Breadstick-Innovations/M4-Breadstick/Examples/4. Button/IMG_8299.JPG

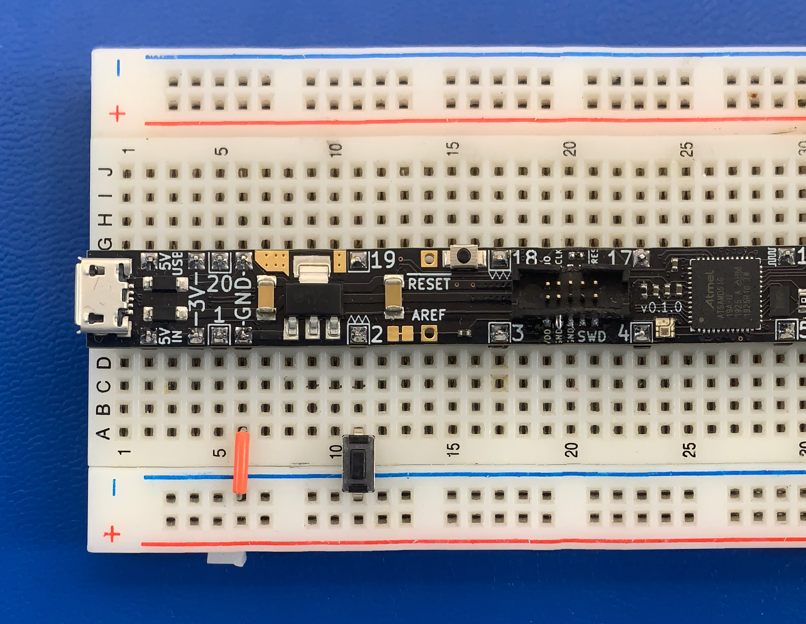
Examples/4. Button/IMG_8299.JPG
