Breadstick-Innovations/M4-Breadstick/Examples/5. Dual I2C Display/IMG_3248.jpg

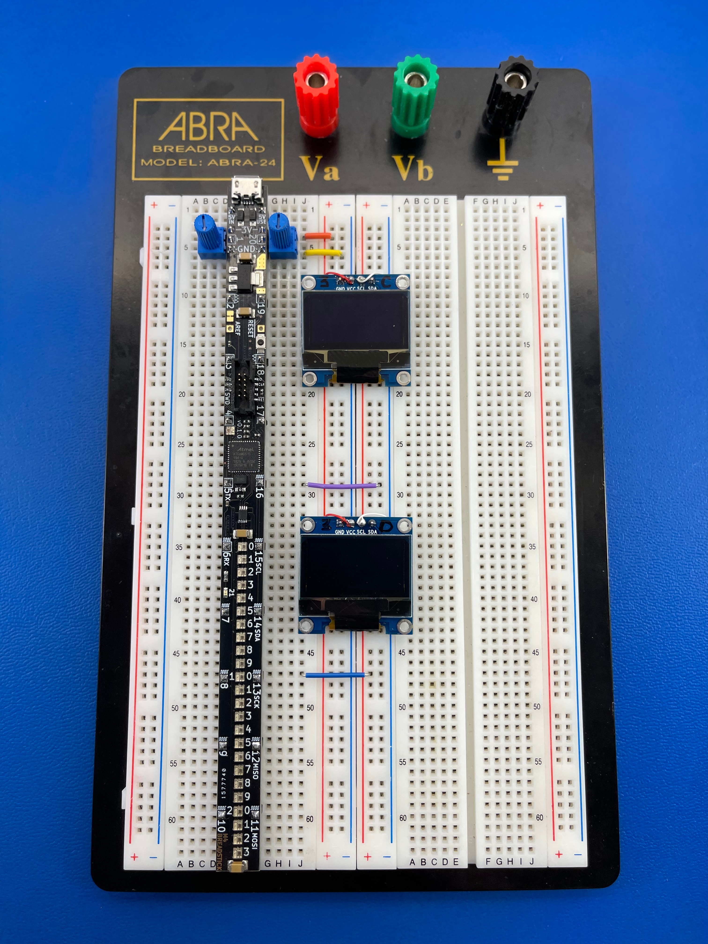
Examples/5. Dual I2C Display/IMG_3248.jpg
