Breadstick-Innovations/M4-Breadstick/Examples/6. Many Pots/IMG_8300.JPG

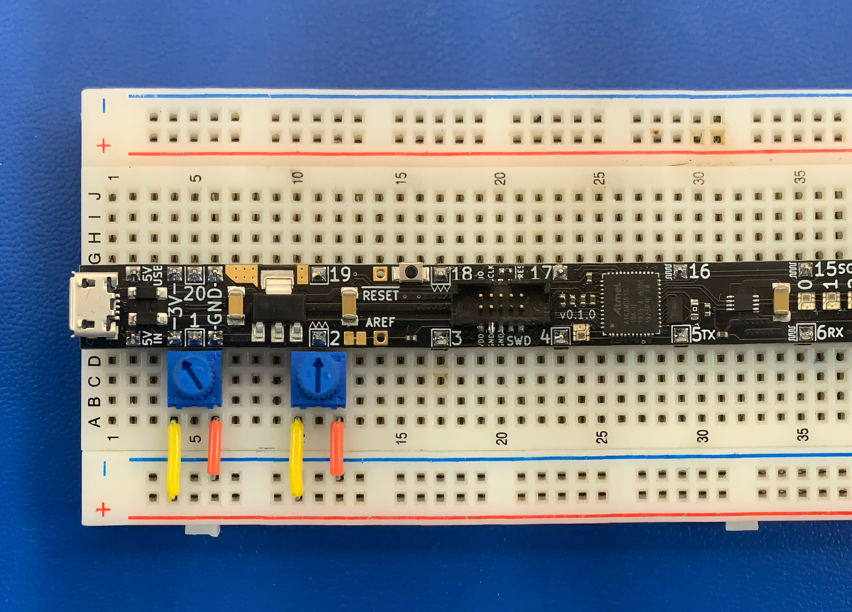
Examples/6. Many Pots/IMG_8300.JPG
