Breadstick-Innovations/M4-Breadstick/Examples/7. Many Buttons/IMG_8317.JPG

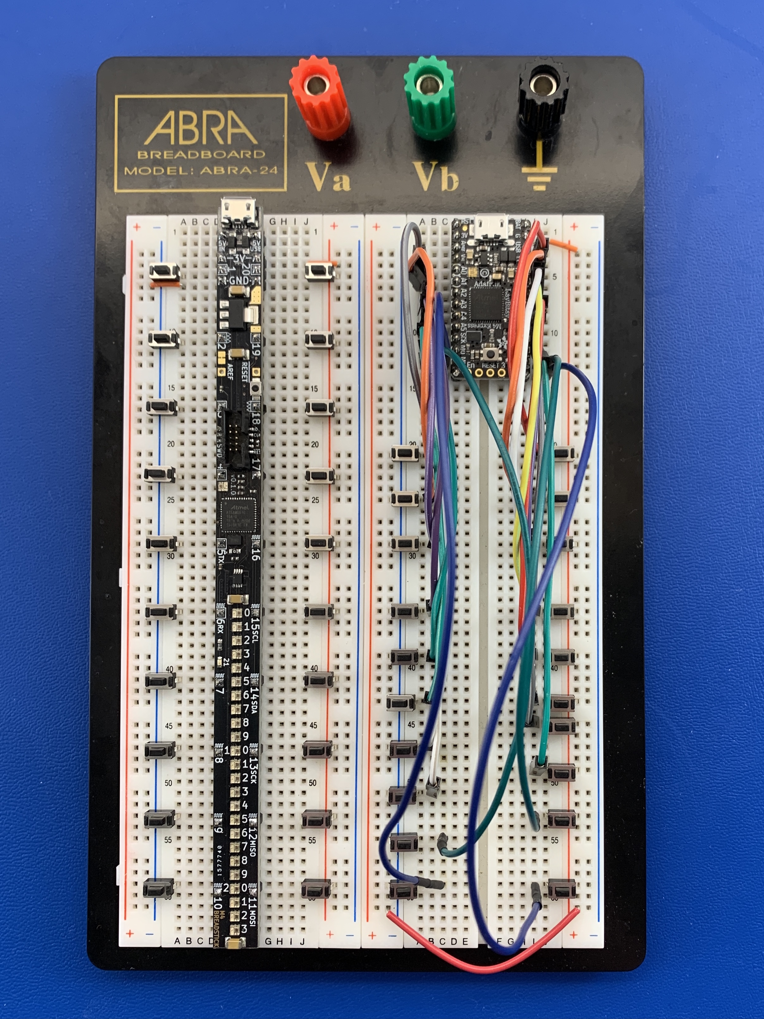
Examples/7. Many Buttons/IMG_8317.JPG
