Breadstick-Innovations/M4-Breadstick/Examples/PowerRails.JPG

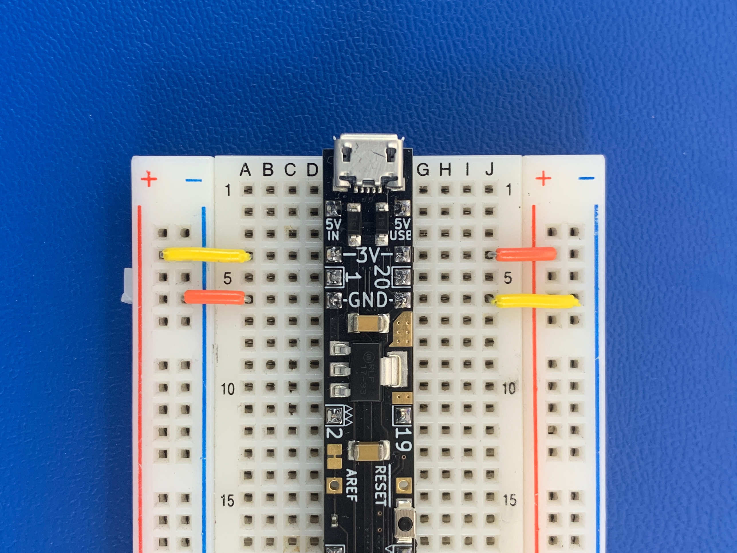
Examples/PowerRails.JPG
